project-neon/Esguicho/Software/Tests/TESTE-INSPECAO/TESTE-INSPECAO.ino

//Bibliotecas internas
#include "config.h"
#include "motors.h"
#include "controller_IR.h"

unsigned long LedCounter = millis();

void setup(){
  Serial.begin(115200);
  controllerInit();
  motorsInit();
}

void loop() {
  controllerIR();

  if(stage == 1) {
    if((millis() - LedCounter) < 300) digitalWrite(2, HIGH); // Acende o led do pino 2
    else digitalWrite(2, LOW); // Apaga o led do pino 2
    if((millis() - LedCounter) > 600) LedCounter = millis(); // Verifica se já passou 600 milisegundos
  }
  else if(stage == 2) {
    digitalWrite(2, HIGH);
    speedL = 60;
    speedR = 60;
    motorsOutput();
  } else {
    digitalWrite(2, LOW);
    speedL = speedR = 0;
    motorsOutput();
  }
  Serial.print("speedL: ");
  Serial.print(speedL);
  Serial.print("\t");
  Serial.print("speedR: ");
  Serial.print(speedR);
  Serial.println("\t\t");
}
